AEFeinstein/gbaZero/Images/adjustments.png

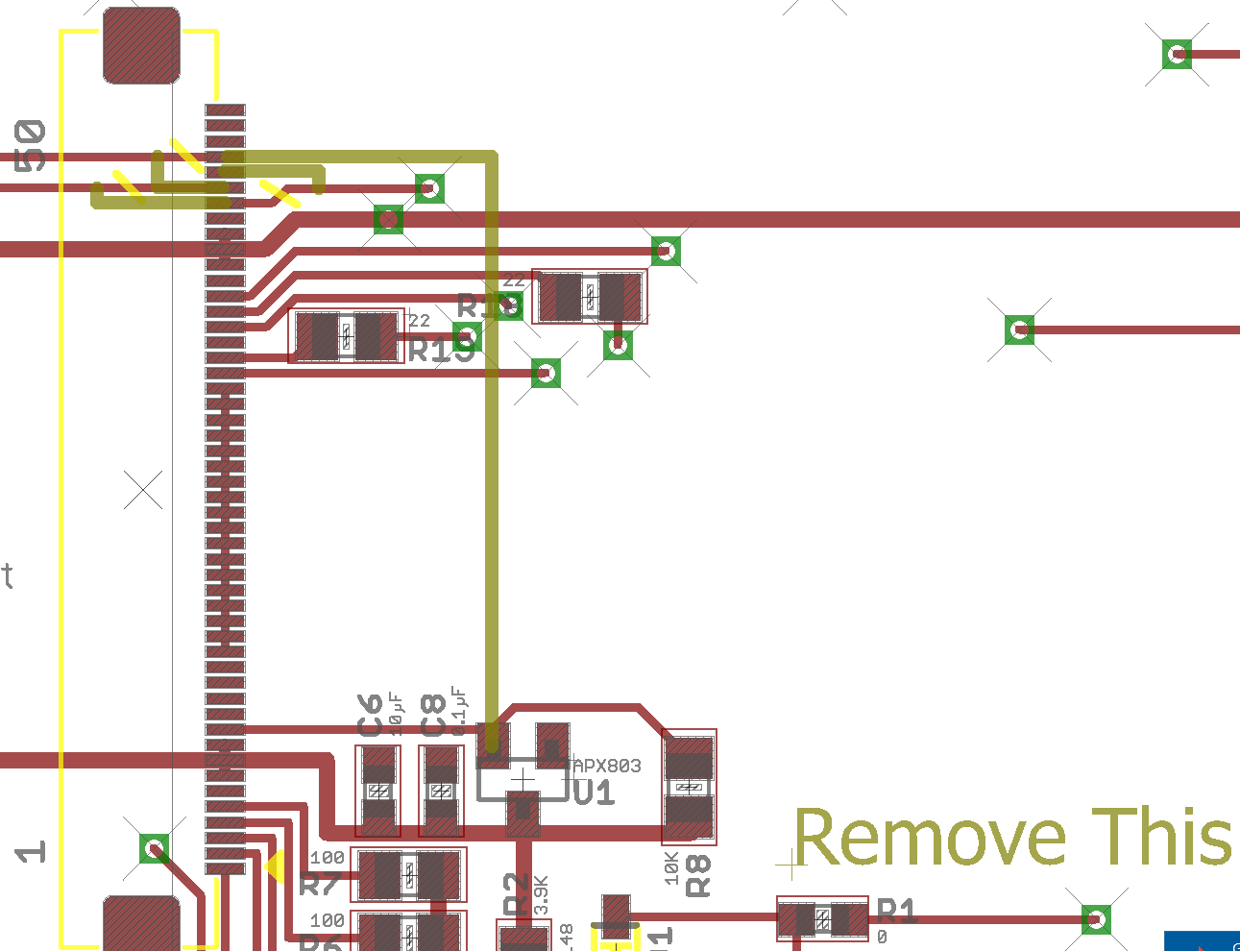
Images/adjustments.png
