AEFeinstein/gbaZero/Images/Assembly/07 - Display Connector.jpg

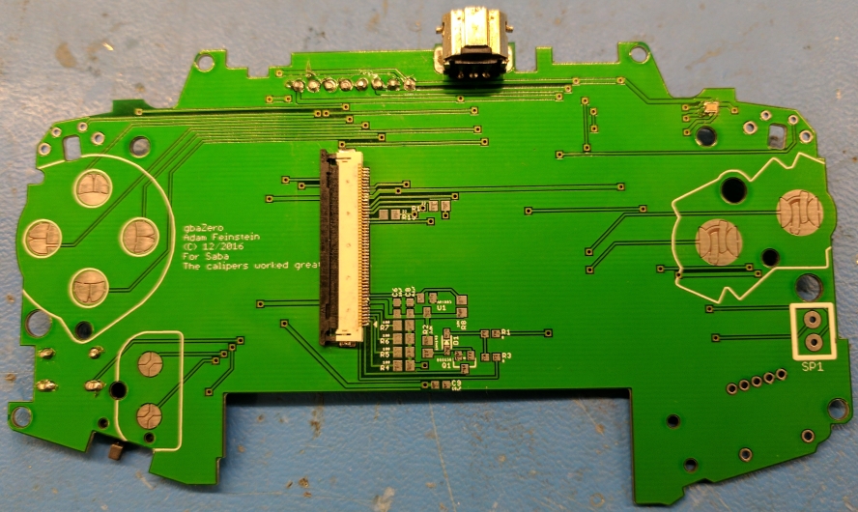
Images/Assembly/07 - Display Connector.jpg
