AEFeinstein/gbaZero/Images/Assembly/09 - Display Connector Microscope.jpg

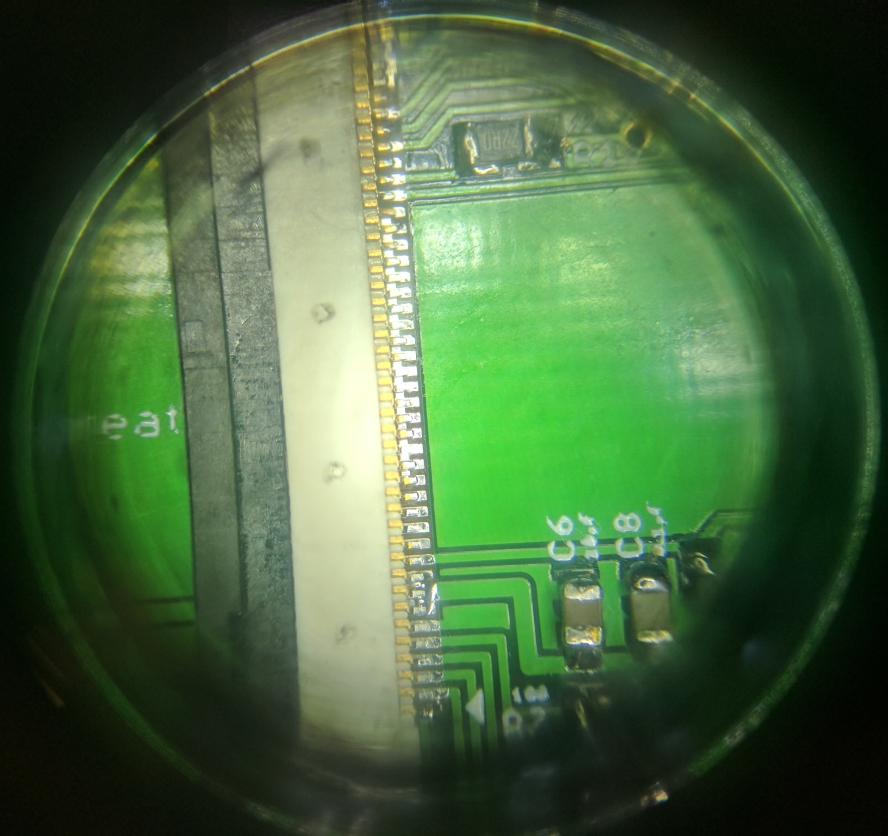
Images/Assembly/09 - Display Connector Microscope.jpg
