AEFeinstein/gbaZero/Images/Assembly/24 - Cartridge Support Removed.jpg

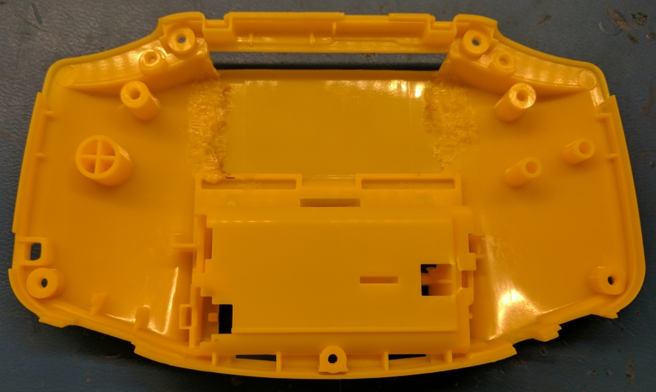
Images/Assembly/24 - Cartridge Support Removed.jpg
