AEFeinstein/gbaZero/Images/Assembly/26 - Display Adhesive.jpg

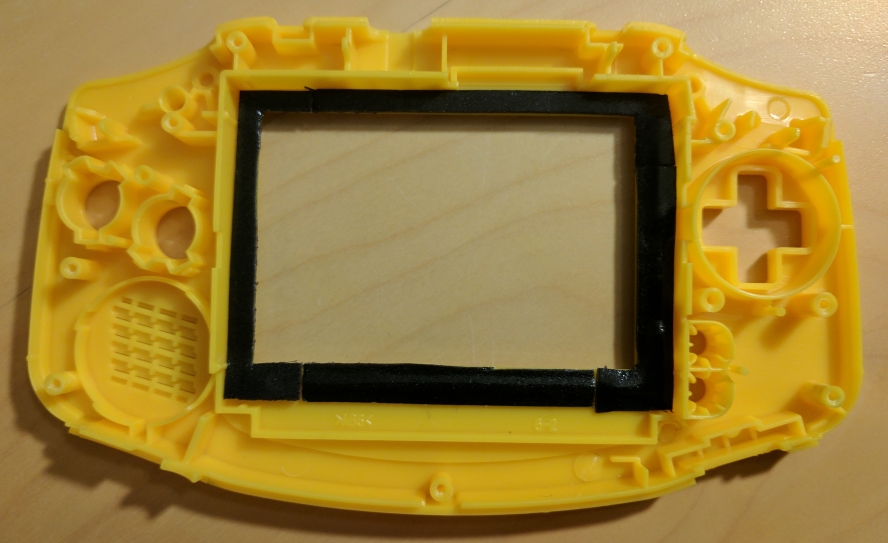
Images/Assembly/26 - Display Adhesive.jpg
